PhotonicTek/Laser-Warning-Sign-Build/images/mockup.png

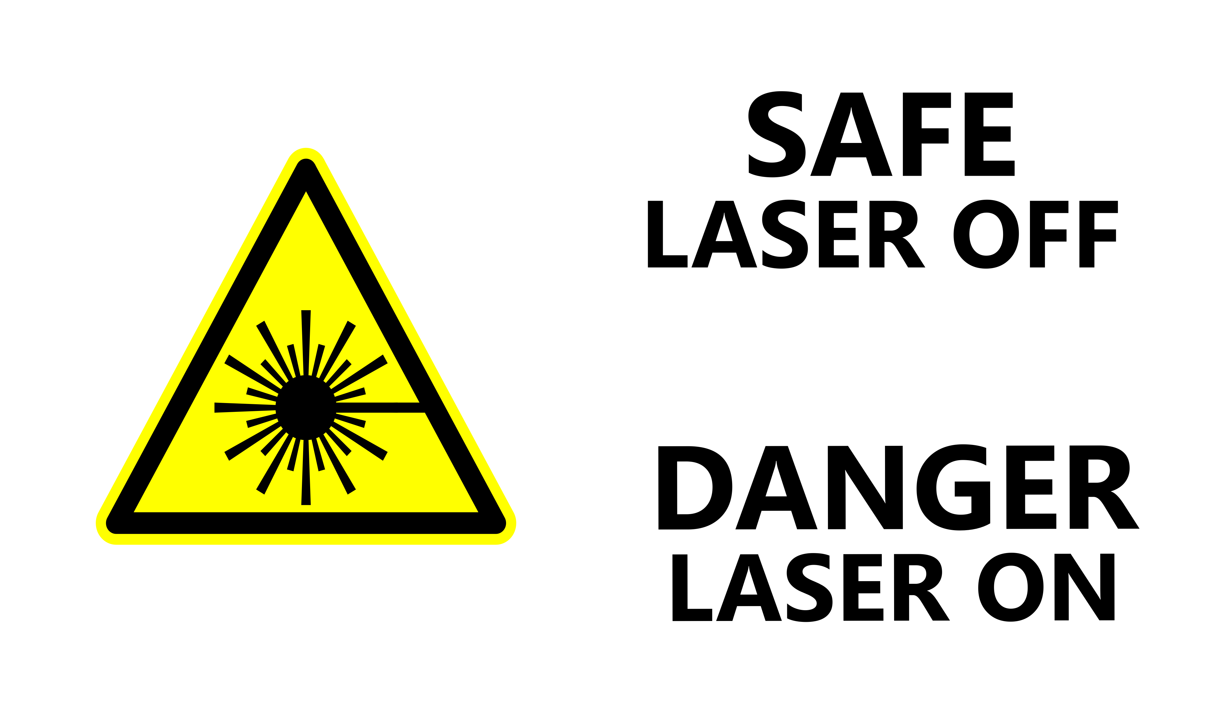
images/mockup.png
