PhotonicTek/Laser-Warning-Sign-Build/images/Video_Asset3.png

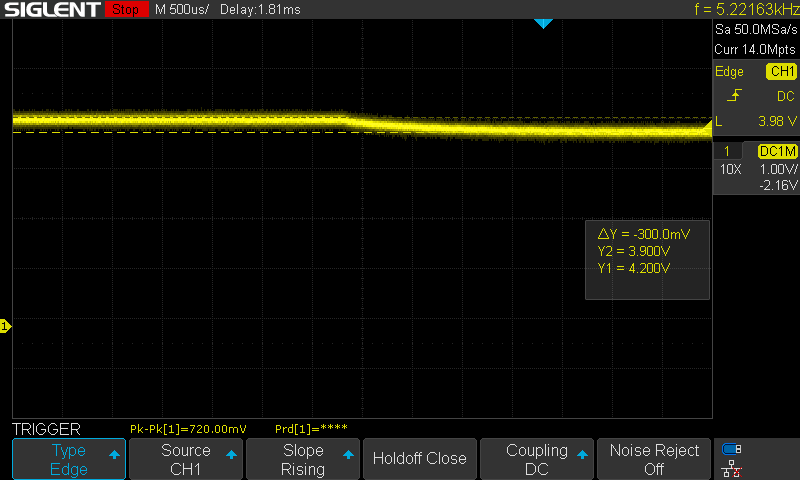
images/Video_Asset3.png
