PhotonicTek/Laser-Warning-Sign-Build/images/Video_Asset4.png

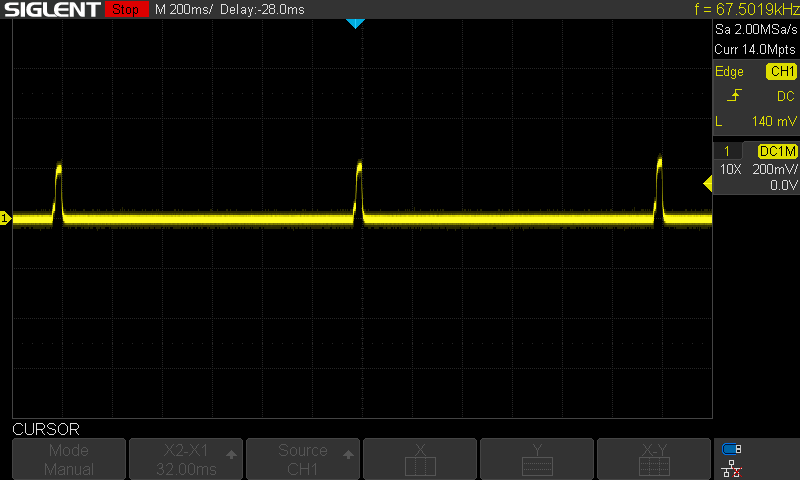
images/Video_Asset4.png
